Jim-shop/SmartRubbishBin/CarModel/滑槽板（最外））.SLDPRT

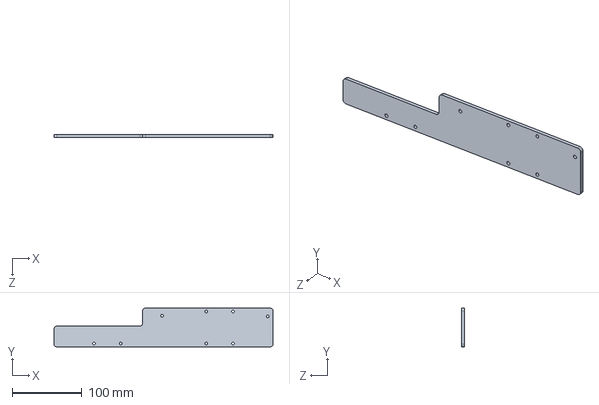
[picture p15: CAD file, 2022-10-22]
CarModel/滑槽板（最外））.SLDPRT
315.0 x 56.0 x 4.00 mm
