Jim-shop/SmartRubbishBin/CarModel/滑槽板（中间）.SLDPRT

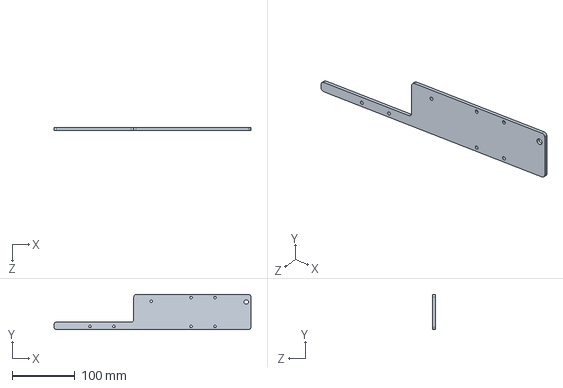
[picture p16: CAD file, 2022-10-22]
CarModel/滑槽板（中间）.SLDPRT
315.0 x 56.0 x 4.00 mm
