Jim-shop/SmartRubbishBin/CarModel/角铁2.SLDPRT

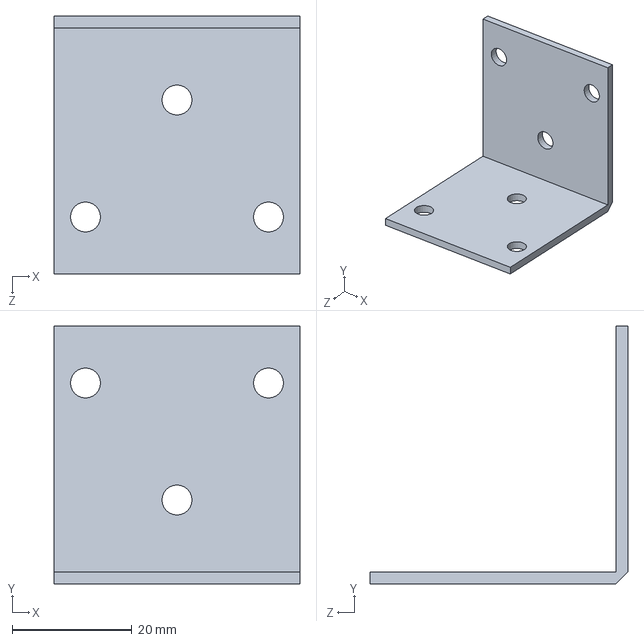
[picture p17: CAD file, 2022-10-22]
CarModel/角铁2.SLDPRT
41.0 x 43.0 x 43.0 mm
