Jim-shop/SmartRubbishBin/CarModel/钢管.SLDPRT

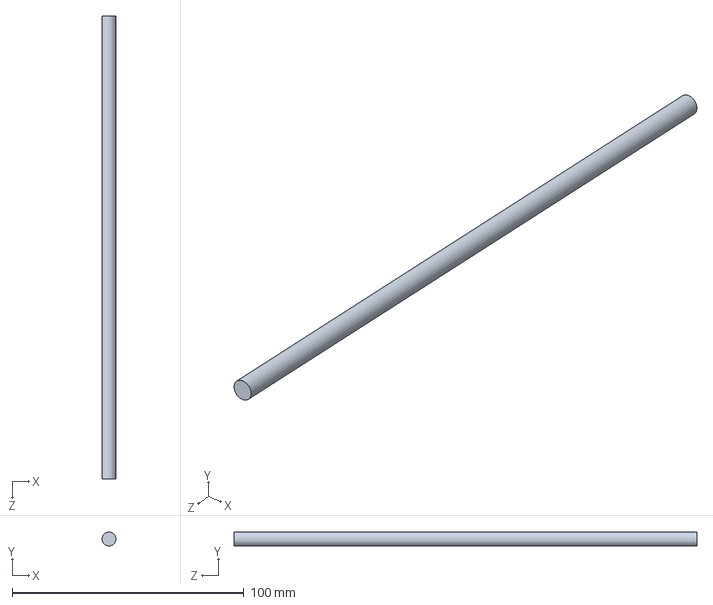
[picture p18: CAD file, 2022-10-22]
CarModel/钢管.SLDPRT
6.00 x 6.00 x 200.0 mm
