Jim-shop/SmartRubbishBin/CarModel/连杆2.SLDPRT

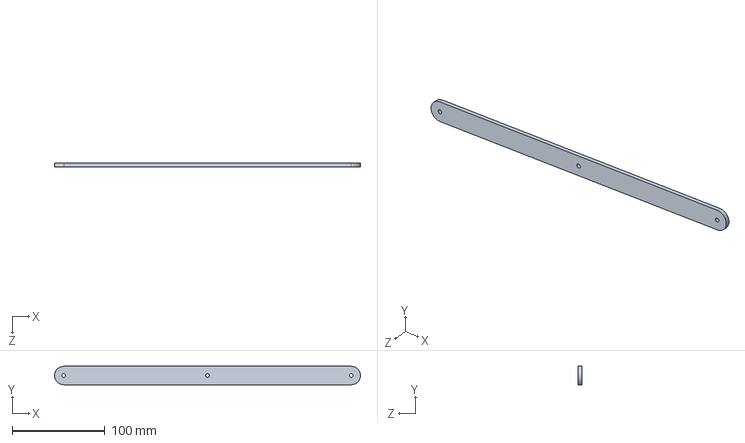
[picture p19: CAD file, 2022-10-22]
CarModel/连杆2.SLDPRT
330.0 x 20.0 x 4.00 mm
