Jim-shop/SmartRubbishBin/CarModel/小车底板.SLDPRT

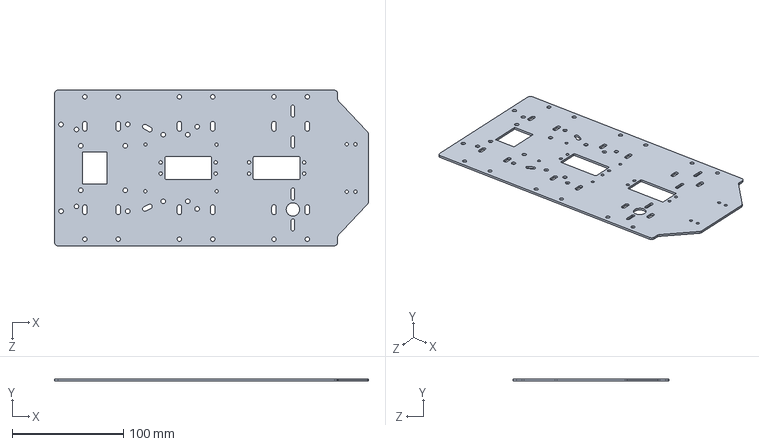
[picture p20: CAD file, 2022-10-22]
CarModel/小车底板.SLDPRT
282.3 x 2.00 x 140.0 mm
