Jim-shop/SmartRubbishBin/CarModel/杆.SLDPRT

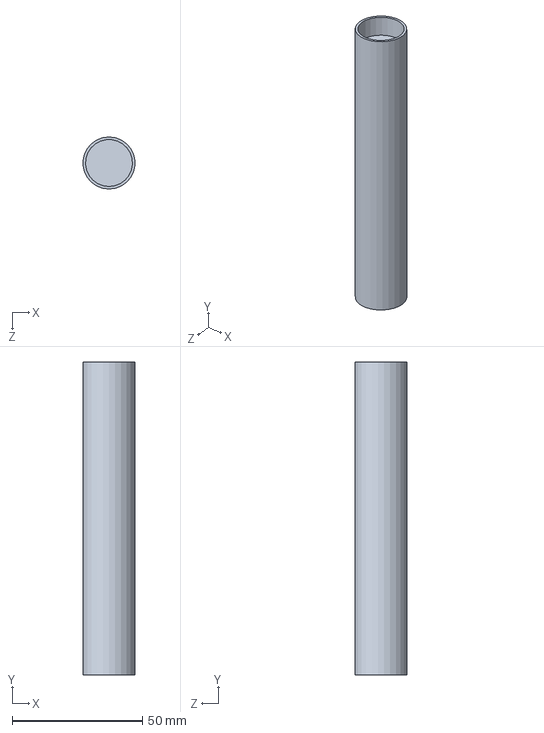
[picture p21: CAD file, 2022-10-22]
CarModel/杆.SLDPRT
19.9 x 120.0 x 20.0 mm
