Jim-shop/SmartRubbishBin/CarModel/底座.SLDPRT

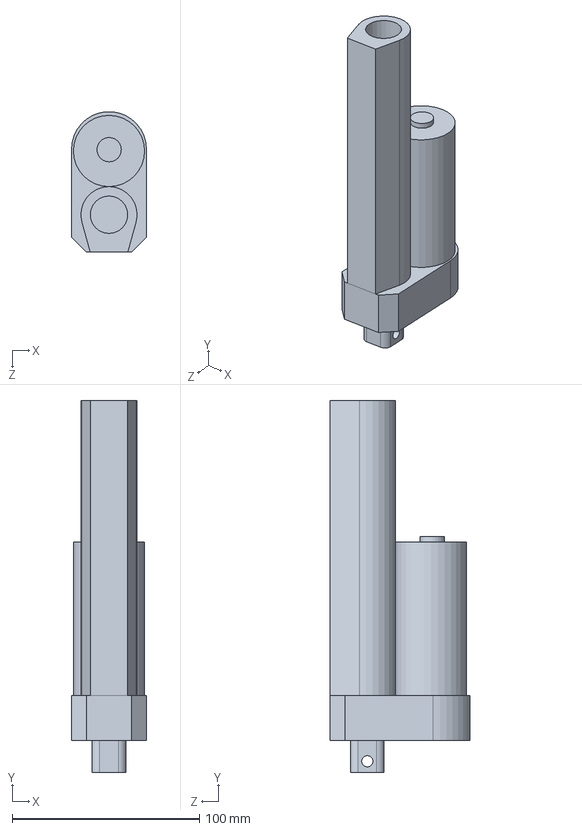
[picture p22: CAD file, 2022-10-22]
CarModel/底座.SLDPRT
40.0 x 198.5 x 74.9 mm
