Jim-shop/SmartRubbishBin/CarModel/塞打螺栓.SLDPRT

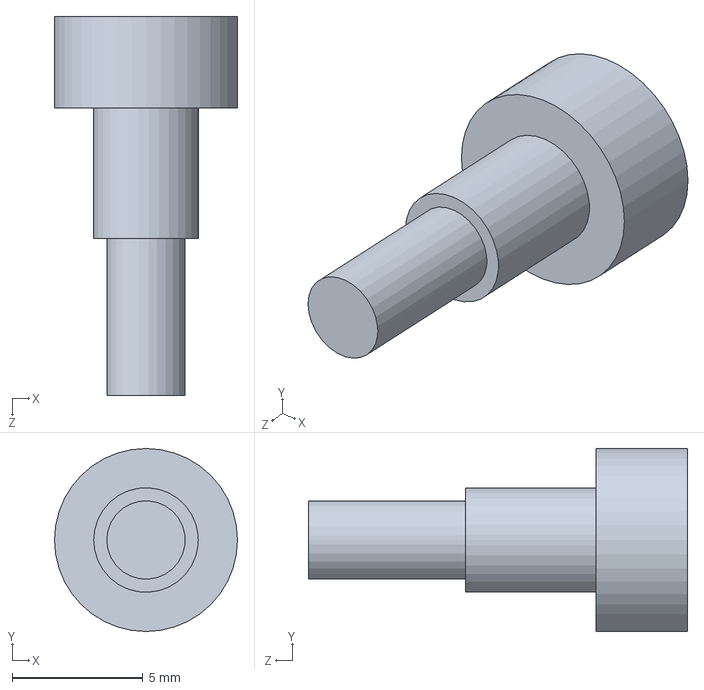
[picture p23: CAD file, 2022-10-22]
CarModel/塞打螺栓.SLDPRT
7.00 x 7.00 x 14.5 mm
