Jim-shop/SmartRubbishBin/CarModel/角铁1.SLDPRT

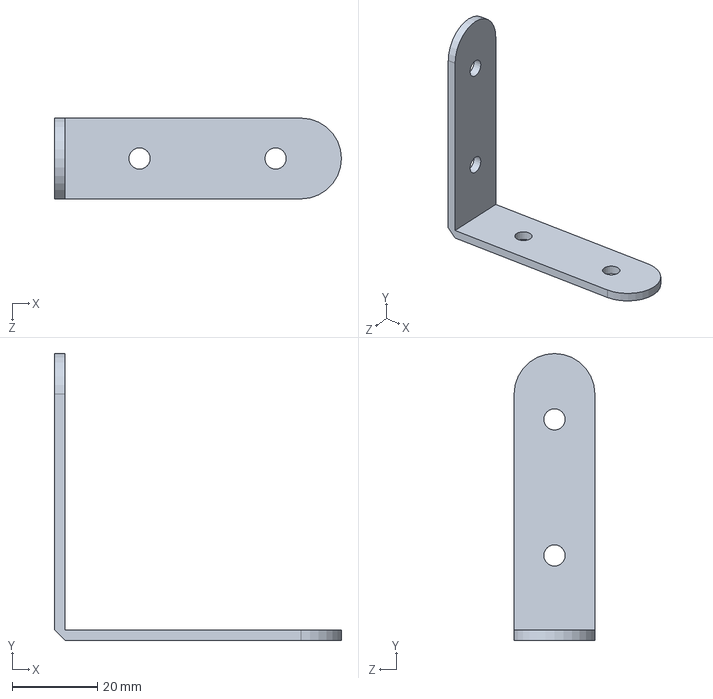
[picture p24: CAD file, 2022-10-22]
CarModel/角铁1.SLDPRT
67.5 x 67.5 x 19.0 mm
