Jim-shop/SmartRubbishBin/CarModel/倾倒杆2.SLDPRT

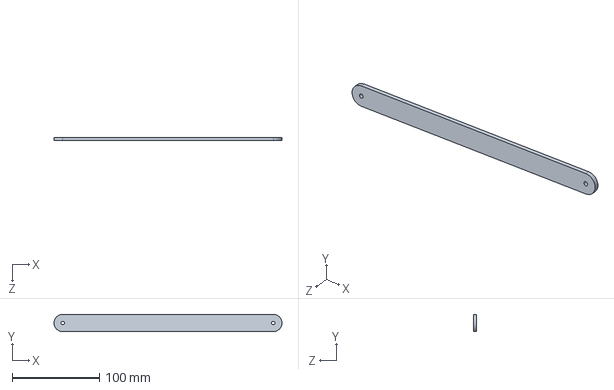
[picture p25: CAD file, 2022-10-22]
CarModel/倾倒杆2.SLDPRT
262.0 x 20.0 x 4.00 mm
