Jim-shop/SmartRubbishBin/CarModel/倾倒杆（叉车）.SLDPRT

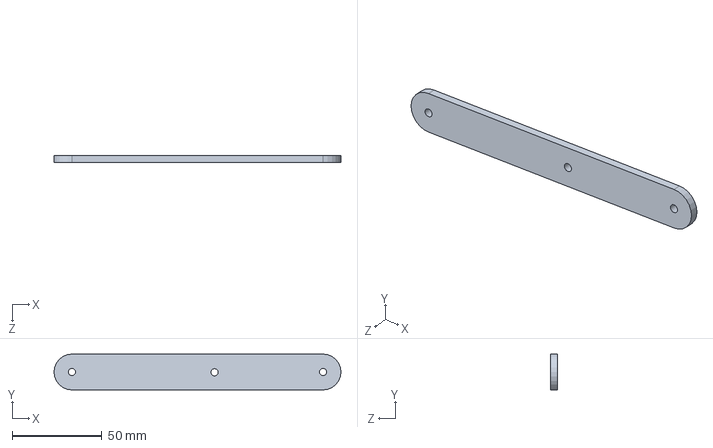
[picture p26: CAD file, 2022-10-22]
CarModel/倾倒杆（叉车）.SLDPRT
160.0 x 20.0 x 4.00 mm
